TylerK07/YM3812-Module/Articles 9_SynthCard/SynthCard_YM3812.kicad_sch

## KiCad design Articles 9_SynthCard/SynthCard_YM3812.kicad_sch (2023-07-27)

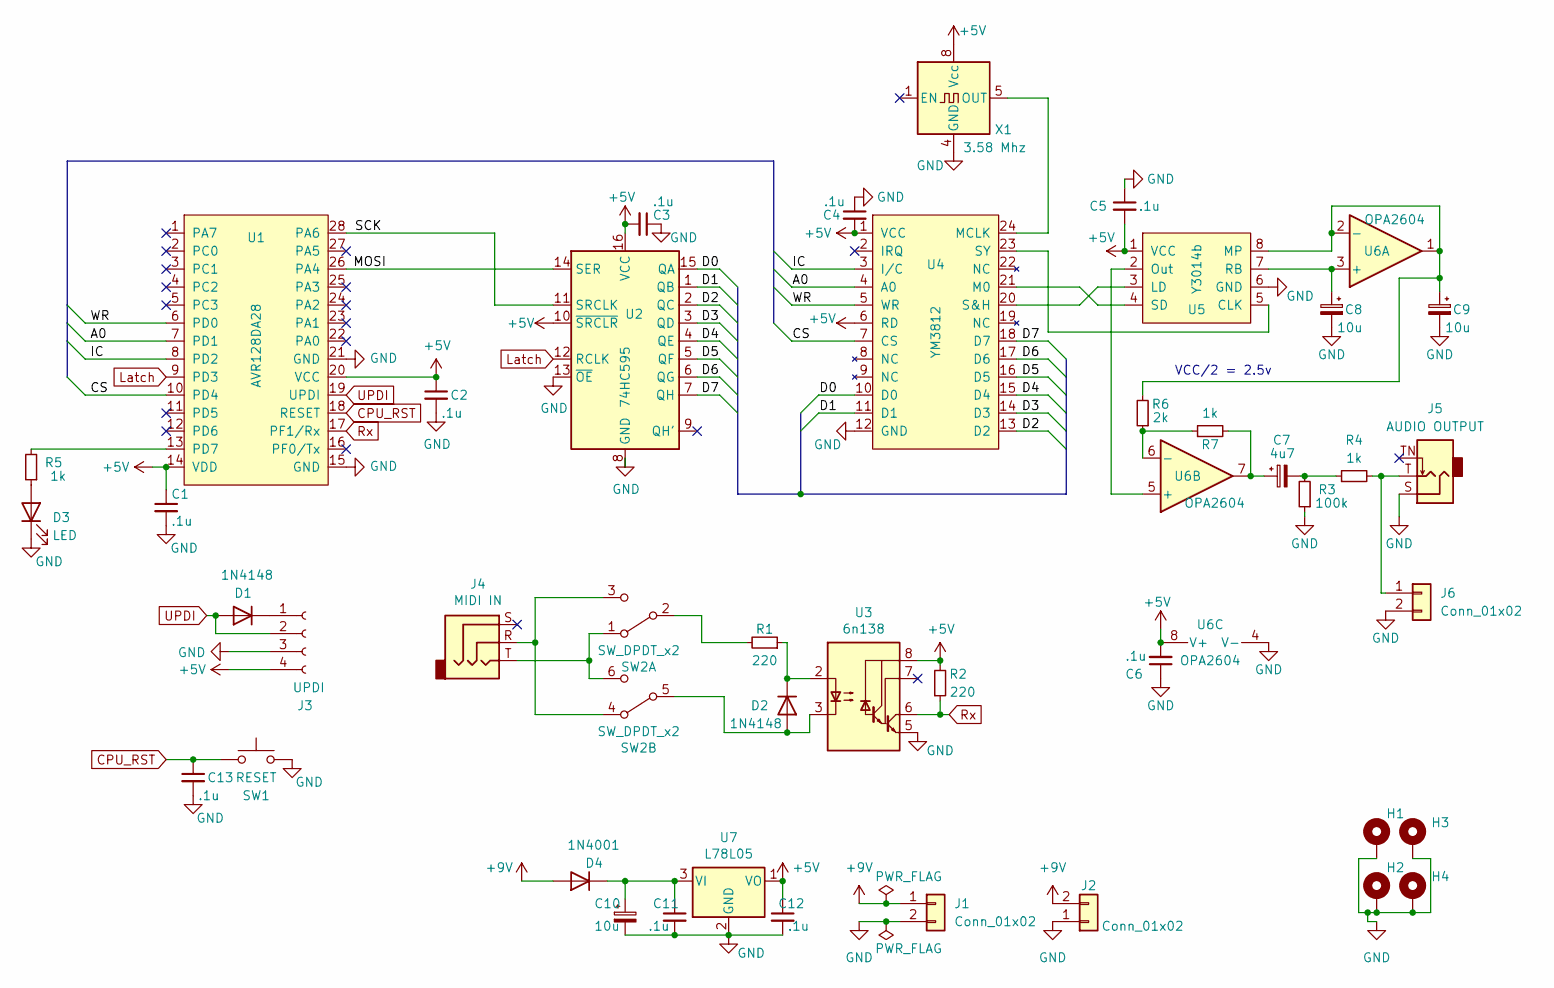
[picture p10: schematic SynthCard_YM3812.kicad_sch]

Parts:
C1, C2, C3, C4, C5, C6, C11, C12, C13: .1u; C_Disc_D6.0mm_W2.5mm_P5.00mm
C7: 4u7; CP_Radial_D5.0mm_P2.50mm
C8, C9, C10: 10u; CP_Radial_D5.0mm_P2.50mm
D1, D2: 1N4148; D_DO-35_SOD27_P7.62mm_Horizontal
D3: LED; LED_D3.0mm
D4: 1N4001; D_DO-35_SOD27_P7.62mm_Horizontal
H1, H2, H3, H4: MountingHole_Pad; MountingHole_3.2mm_M3_Pad
J1, J2: Conn_01x02; PinHeader_1x02_P2.54mm_Horizontal
J3: UPDI; PinHeader_1x04_P2.54mm_Vertical
J4: MIDI IN; StereoAudio_3.5mm
J5: AUDIO OUTPUT; MonoAudio_3.5mm_SW
J6: Conn_01x02; PinHeader_1x02_P2.54mm_Vertical
R1, R2: 220; R_Axial_DIN0207_L6.3mm_D2.5mm_P7.62mm_Horizontal
R3: 100k; R_Axial_DIN0207_L6.3mm_D2.5mm_P7.62mm_Horizontal
R4, R5, R7: 1k; R_Axial_DIN0207_L6.3mm_D2.5mm_P7.62mm_Horizontal
R6: 2k; R_Axial_DIN0207_L6.3mm_D2.5mm_P7.62mm_Horizontal
SW1: RESET; SW_PUSH_6mm
SW2: SW_DPDT_x2; SW_E-Switch_EG1271_DPDT
U1: AVR128DA28; DIP-28_W7.62mm_Socket_LongPads
U2: 74HC595; DIP-16_W7.62mm_Socket_LongPads
U3: 6n138; DIP-8_W7.62mm_LongPads
U4: YM3812; DIP-24_W15.24mm_Socket_LongPads
U5: Y3014b; DIP-8_W7.62mm_Socket_LongPads
U6: OPA2604; DIP-8_W7.62mm_Socket_LongPads
U7: L78L05; TO-92_HandSolder
X1: 3.58 Mhz; Oscillator_DIP-8

Connections:
+5V: C1.1, C2.1, C3.2, C4.2, C5.2, C6.2, C12.1, J3.4, R2.2, U1.14 (VDD), U1.20 (VCC), U2.10 (~SRCLR), U2.16 (VCC), U3.8 (VCC), U4.1 (VCC), U4.6 (RD), U5.1 (VCC), U6.8 (V+), U7.1 (VO), X1.8 (Vcc)
+9V: D4.2 (A), J1.1, J2.2
A0: U1.7 (PD1), U4.4 (A0)
CPU_RST: C13.1, SW1.2, U1.18 (RESET)
CS: U1.10 (PD4), U4.7 (CS)
D0: U2.15 (QA), U4.10 (D0)
D1: U2.1 (QB), U4.11 (D1)
D2: U2.2 (QC), U4.13 (D2)
D3: U2.3 (QD), U4.14 (D3)
D4: U2.4 (QE), U4.15 (D4)
D5: U2.5 (QF), U4.16 (D5)
D6: U2.6 (QG), U4.17 (D6)
D7: U2.7 (QH), U4.18 (D7)
GND: C1.2, C2.2, C3.1, C4.1, C5.1, C6.1, C8.2, C9.2, C10.2, C11.2, C12.2, C13.2, D3.1 (K), H1.1, H2.1, H3.1, H4.1, J1.2, J2.1, J3.3, J5.S, J6.2, R3.1, SW1.1, U1.15 (GND), U1.21 (GND), U2.8 (GND), U2.13 (~OE), U3.5 (GND), U4.12 (GND), U5.6 (GND), U6.4 (V-), U7.2 (GND), X1.4 (GND)
IC: U1.8 (PD2), U4.3 (I/C)
Latch: U1.9 (PD3), U2.12 (RCLK)
MOSI: U1.26 (PA4), U2.14 (SER)
unnamed: C7.1, R7.2, U6.7
unnamed: C7.2, R3.2, R4.1
unnamed: C8.1, U5.7 (RB), U6.3 (+)
unnamed: C9.1, R6.2, U5.8 (MP), U6.1, U6.2 (-)
unnamed: C10.1, C11.1, D4.1 (K), U7.3 (VI)
unnamed: D1.1 (K), J3.1
unnamed: D2.1 (K), R1.1, U3.2 (C1)
unnamed: D2.2 (A), SW2.5 (B), U3.3 (C2)
unnamed: D3.2 (A), R5.1
unnamed: J4.R, SW2.3 (C), SW2.4 (A)
unnamed: J4.T, SW2.1 (A), SW2.6 (C)
unnamed: J5.T, J6.1, R4.2
unnamed: R1.2, SW2.2 (B)
unnamed: R5.2, U1.13 (PD7)
unnamed: R6.1, R7.1, U6.6 (-)
unnamed: U4.20 (S&H), U5.3 (LD)
unnamed: U4.21 (M0), U5.4 (SD)
unnamed: U4.23 (SY), U5.5 (CLK)
unnamed: U4.24 (MCLK), X1.5 (OUT)
unnamed: U5.2 (Out), U6.5 (+)
Rx: R2.1, U1.17 (PF1/Rx), U3.6 (VO2)
SCK: U1.28 (PA6), U2.11 (SRCLK)
UPDI: D1.2 (A), J3.2, U1.19 (UPDI)
WR: U1.6 (PD0), U4.5 (WR)

Notes on the sheet:
VCC/2 = 2.5v
