TylerK07/YM3812-Module/Articles 10_PitchWheel/YM3812_PitchWheel/YM3812.cpp

/*
     _____.___.  _____  ________    ______  ____________
     \__  |   | /     \ \_____  \  /  __  \/_   \_____  \
      /   |   |/  \ /  \  _(__  <  >      < |   |/  ____/
      \____   /    Y    \/       \/   --   \|   /       \
      / ______\____|__  /______  /\______  /|___\_______ \
      \/              \/       \/        \/             \/
            ________ __________.____    ________
            \_____  \\______   \    |   \_____  \
             /   |   \|     ___/    |    /  ____/
            /    |    \    |   |    |___/       \
            \_______  /____|   |_______ \_______ \
                    \/                 \/       \/


YM3182 OPL2 LIBRARY source code designed to run on the AVR128DA28.
Copyright (C) 2022 Tyler Klein

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
Description:
This library wraps Yamaha's YM3812 sound processor with functions that allow for
direct manipulation of the chip's registers so you can build cool things like EuroRack modules!

*/

#include "Arduino.h"
#include <SPI.h>
#include "YM3812.h"


//Port Bits defined for control bus:
#define YM_WR    0b00000001                                                    // Pin 0, Port D - Write
#define YM_A0    0b00000010                                                    // Pin 1, Port D - Differentiates between address and data
#define YM_IC    0b00000100                                                    // Pin 2, Port D - Reset Pin
#define YM_LATCH 0b00001000                                                    // Pin 3, Port D - Output Latch
#define YM_CS    0b00010000                                                    // Pin 4, Port D - Left YM3812 Chip Select

// Optional debug light shows when information gets written to the YM3812
#define DATA_LED 0b10000000                                                    // We can use this to see activity when data is being sent

/**************
* Constructor *
**************/

YM3812::YM3812(){                                                              // Constructor
}


void YM3812::setBendRange(uint8_t wheelNoteRange){                             // Pass the number of notes in the range (even numbers please!)
  if( wheelNoteRange < 2 ) return;
  bend_note_offset = wheelNoteRange >> 1;                                      // Divide wheel range by 2 to get the offset
  bend_note_size   = PITCH_WHEEL_RANGE / (wheelNoteRange & 0xFFFE);            // Divide full range by number of notes (force to be even number of notes)
}



/************************
* Patch Functions       *
************************/

void YM3812::patchNoteOn( PatchArr &patch, uint8_t midiNote, uint8_t velocity, uint16_t pitchBend ){
  last_channel = chGetNext();
  channel_states[ last_channel ].pPatch  = &patch;                             // Store pointer to the patch
  channel_states[ last_channel ].midi_note  = midiNote;                        // Store midi note associated with the channel
  channel_states[ last_channel ].velocity = velocity;                          // Store velocity associated with the channel
  channel_states[ last_channel ].note_state = true;                            // Indicate that the note is turned on
  channel_states[ last_channel ].state_changed = millis();                     // save the time that the note was turned on

  if( pitchBend == 0x2000 ){                                                   // When not in use, do this the easy way
    channel_states[ last_channel ].bend_note = 0;                              // no pitch bend, so bend_note is just zero
    channel_states[ last_channel ].bend_rem = 0;                               // no pitch bend, so bend_rem is just zero
  } else {                                                                     // When pitchBend is set, calculate the new values
    channel_states[ last_channel ].bend_note = (pitchBend / bend_note_size) - bend_note_offset; // Calculate the whole number of semitones to bend
    channel_states[ last_channel ].bend_rem = pitchBend % bend_note_size;      // Calculate the remaining portion of a semitone to bend
  }

  chPlayNote( last_channel );                                                  // Play the note on the correct YM3812 channel
}


void YM3812::patchNoteOn( PatchArr &patch, uint8_t midiNote, uint8_t velocity ){ // If pitch bend value not passed, assume a pitch bend in the middle
  patchNoteOn( patch, midiNote, velocity, 0x2000 ); 
}


void YM3812::patchNoteOff( PatchArr &patch, uint8_t midiNote ){
  for( uint8_t ch = 0; ch<num_channels; ch++ ){
    if( channel_states[ch].pPatch == &patch ){
      if( channel_states[ch].midi_note == midiNote ){
        channel_states[ ch ].state_changed = millis();                         // Save the time that the state changed
        channel_states[ ch ].note_state = false;                               // Indicate that the note is currently off
        regKeyOn( ch, 0 );                                                     // Turn off any channels associated with the midiNote
      }
    }
  }
}

void YM3812::patchAllOff( PatchArr &patch ){
  for( uint8_t ch = 0; ch<num_channels; ch++ ){
    if( channel_states[ch].pPatch == &patch ){
      channel_states[ ch ].state_changed = millis();                           // Save the time that the state changed
      channel_states[ ch ].note_state = false;                                 // Indicate that the note is currently off
      regKeyOn( ch, 0 );                                                       // Turn off any channels associated with the midiNote
    }
  }
}

void YM3812::patchUpdate( PatchArr &patch ){                                   // Update the patch data of any active channels assocaited with the patch
  for( byte ch = 0; ch < num_channels; ch++ ){                                 // Loop through each channel
    if( channel_states[ch].pPatch == &patch ) chSendPatch( ch, patch );        // If the channel uses the patch, update the patch data on the chip
  }
}

void YM3812::patchPitchBend( PatchArr &patch, uint16_t pitchBend){             // Update the pitch of all notes associated with patch based on pitchBend
  for( byte ch = 0; ch < num_channels; ch++ ){                                 // Loop through each channel
    if( channel_states[ch].pPatch == &patch ){
      if( pitchBend == 0x2000 ){                                               // When not in use, do this the easy way
        channel_states[ ch ].bend_note = 0;                                    // no pitch bend, so bend_note is just zero
        channel_states[ ch ].bend_rem = 0;                                     // no pitch bend, so bend_rem is just zero
      } else {                                                                 // When pitchBend is set, calculate the new values
        channel_states[ ch ].bend_note = (pitchBend / bend_note_size) - bend_note_offset; // Calculate the whole number of semitones to bend
        channel_states[ ch ].bend_rem = pitchBend % bend_note_size;            // Calculate the remaining portion of a semitone to bend
      }
      chSetPitch(ch);
    }
  }
}


/************************
* Channel Functions     *
************************/

// chSendPatch Theory of Operation:
// This function is the heart of the class, and without too many modifications can be updated to work with any of the
// Yamaha synthesis chips. The function accepts a generalized patch array with values in order according to the
// indicies outlined in YMDefs.h. Because all values in the array are between 0 and 127, this function scales
// those values to the correct bit depth, combines them with other values to produce the correct combinations for the register
// map of the YM3812 and then sends them to the sound chip.

void YM3812::chSendPatch( byte ch, PatchArr &patch ){
  uint8_t  mem_offset, patch_offset;
  uint8_t  op_level;

  //Channel Settings
  sendData( 0xC0+ch,  ((patch[PATCH_FEEDBACK]>>4)<<1) |                        // Compose the feedback and Algorithm values
                       (patch[PATCH_ALGORITHM]>>6)    );                       // into a single byte and send to YM3812

  for( uint8_t op = 0; op<2; op++ ){
    mem_offset = op_map[channel_map[ch] + op*3];                               // Determine memory offset for slot 1 for the channel
    patch_offset = PATCH_OP_SETTINGS * op;                                     // Determine operator's index offset for the patch properties 

    if( (patch[PATCH_ALGORITHM] == 0) && (op==0) ){
      op_level = patch[patch_offset + PATCH_LEVEL] >> 1;
    } else {
      op_level = 63-( ( (127 - patch[patch_offset + PATCH_LEVEL]) * channel_states[ ch ].velocity ) >> 8);
    }

    sendData( 0x20+mem_offset,      ((patch[patch_offset + PATCH_TREMOLO        ]>>6)<<7) |  // Compose Tremolo, vibrato, percussive envelope
                                    ((patch[patch_offset + PATCH_VIBRATO        ]>>6)<<6) |  // envelope scaling flags along with frequency
                                    ((patch[patch_offset + PATCH_PERCUSSIVE_ENV ]>>6)<<5) |  // multiple into a single 8-bit register value
                                    ((patch[patch_offset + PATCH_ENV_SCALING    ]>>6)<<4) |  // and send to the YM3812
                                    ((patch[patch_offset + PATCH_FREQUENCY_MULT ]>>3)<<0) );

    sendData( 0x40+mem_offset,      ((patch[patch_offset + PATCH_LEVEL_SCALING ]>>5)<<6)  |  // Compose level scaling and level value for the
                                      op_level                                            ); // output channel and send to the YM3812
    sendData( 0x60+mem_offset,      ((patch[patch_offset + PATCH_ATTACK        ]>>3)<<4)  |  // Compose attack and decay settings into a single
                                    ((patch[patch_offset + PATCH_DECAY         ]>>3)<<0)  ); // 8-bit register and send to YM3812
    sendData( 0x80+mem_offset, ((0xF-(patch[patch_offset + PATCH_SUSTAIN_LEVEL ]>>3))<<4) |  // Compose sustain level (inverted) and release rate settings into a single
                                    ((patch[patch_offset + PATCH_RELEASE_RATE  ]>>3)<<0) );  // 8-bit register and send to YM3812
    sendData( 0xE0+mem_offset,      ((patch[patch_offset + PATCH_WAVEFORM      ]>>5)<<0) );  // Send waveform register to YM3812
  }

}

uint8_t YM3812::chGetNext(){
  uint8_t on_channel = 0xFF;                                                   // The channel that has been on the longest 
  uint8_t off_channel = 0xFF;                                                  // The channel that has been OFF the longest
  unsigned long oldest_on_time = millis(); 
  unsigned long oldest_off_time = millis(); 

  for( uint8_t ch=0; ch < num_channels; ch++ ){                                // Loop through all of the channels
    if( channel_states[ch].note_state ){                                       // If the note is turned on...
      if( channel_states[ch].state_changed < oldest_on_time ){                 // Is this the longest running note?
        oldest_on_time = channel_states[ch].state_changed;                     // save the current time
        on_channel = ch;                                                       // save this as our longest running channel
      } 
    } else {                                                                   // If the note is turned off...
      if( channel_states[ch].state_changed < oldest_off_time ){                // Is this the longest turned off note?
        oldest_off_time = channel_states[ch].state_changed;                    // save the current time
        off_channel = ch;                                                      // save this as our longest off channel
      } 
    }
  }

  if( off_channel < 0xFF ){                                                    // If it isn't FF, then we changed... so at least one channel is currently off.
    return( off_channel );                                                     // Return the channel that has been off the longest
  }
  return( on_channel );                                                        // Return the channel that has been ON the longest
}

void YM3812::chSetPitch( uint8_t ch ){
  uint8_t block, fNumIndex;
  uint8_t midiNote = channel_states[ch].midi_note+channel_states[ch].bend_note;// Calculate the midiNote based on the pitchBend data for the midi channel

  if( midiNote > 127 ) midiNote = 0;                                           // If midiNote wrapped around, then PB went below midiNote zero
  if( midiNote > 113 ) return;                                                 // Ignore any midi notes outside the range of the chip
  
  if( midiNote < 18 ){                                                         // For case where midi note is less than our repeating range
    block = 0;                                                                 // Block will always be zero
    fNumIndex = midiNote;                                                      // The midiNote will be the index of the FREQ_SCALE array
  } else {                                                                     // 
    block = (midiNote - 18) / 12;                                              // Calculate the block based on the octave of the note
    fNumIndex = ((midiNote - 18) % 12) + 18;                                   // Calculate the fNum of the note
  }

  uint16_t lFNum = FRQ_SCALE[fNumIndex];
  uint16_t hFNum = FRQ_SCALE[fNumIndex+1];
  uint16_t FNum = (uint32_t(hFNum - lFNum) * uint32_t(channel_states[ch].bend_rem)) / bend_note_size + lFNum;

  regFrqBlock( ch, block );                                                    // Send block number to chip
  regFrqFnum(  ch, FNum  );                                                    // Send F-Number to chip
}

void YM3812::chPlayNote( uint8_t ch ){                                         // Play a note on channel ch with pitch midiNote
  //Assumes that midi note and pitch bend properties were all set before running this function
  regKeyOn( ch, 0 );                                                           // Turn off the channel if it is on
  chSendPatch( ch, *channel_states[ch].pPatch );                               // Send the patch to the YM3812
  chSetPitch( ch );                                                            // Set the pitch of the note (pitch info stored in channel_states array)
  regKeyOn( ch, 1 );                                                           // Turn the channel back on
}



/********************************
* Processor Control Functions   *
********************************/

void YM3812::reset(){
  PORTD.DIRSET = YM_IC | YM_A0 | YM_WR | YM_LATCH | YM_CS | DATA_LED;          // Set control lines high to output mode

  PORTD.OUTCLR = YM_LATCH;                                                     // Set the latch low to start
  PORTD.OUTSET = YM_WR | YM_CS;                                                // Set chip select and write lines high
  PORTD.OUTCLR = DATA_LED;                                                     // Turn the data LED off
  
  //Hard Reset the YM3812
  PORTD.OUTCLR = YM_IC; delay(10);                                             // Hard Reset the processor by bringing Initialize / Clear line low
  PORTD.OUTSET = YM_IC; delay(10);                                             // Complete process by bringing line high and allowing a short moment to reset

  SPI.begin();


  //Clear all of our register caches
  reg_01 = reg_08 = reg_BD = 0;                                                // Clear out global settings
  for( uint8_t ch = 0; ch < YM3812_NUM_CHANNELS; ch++ ){                       // Loop through all of the channels
    reg_A0[ch] = reg_B0[ch] = 0;                                               // Set all register info to zero
  }
  regWaveset( 1 );                                                             // Enable all wave forms (not just sine waves)
}

void YM3812::sendData( uint8_t reg, uint8_t val ){
  PORTD.OUTSET = DATA_LED;

  PORTD.OUTCLR = YM_CS;                                                        // Enable the chip
  PORTD.OUTCLR = YM_A0;                                                        // Put chip into register select mode

  SPI.transfer(reg);                                                           // Put register location onto the data bus through SPI port
  PORTD.OUTSET = YM_LATCH;                                                     // Latch register location into the 74HC595
  delayMicroseconds(1);                                                        // wait a tic.
  PORTD.OUTCLR = YM_LATCH;                                                     // Bring latch low now that the location is latched

  PORTD.OUTCLR = YM_WR;                                                        // Bring write low to begin the write cycle
  delayMicroseconds(10);                                                       // Delay so chip completes write cycle
  PORTD.OUTSET = YM_WR;                                                        // Bring write high
  delayMicroseconds(10);                                                       // Delay until the chip is ready to continue

  PORTD.OUTSET = YM_A0;                                                        // Put chip into data write mode

  SPI.transfer(val);                                                           // Put value onto the data bus through SPI port
  PORTD.OUTSET = YM_LATCH;                                                     // Latch the value into the 74HC595
  delayMicroseconds(1);                                                        // wait a tic.
  PORTD.OUTCLR = YM_LATCH;                                                     // Bring latch low now that the value is latched

  PORTD.OUTCLR = YM_WR;                                                        // Bring write low to begin the write cycle
  delayMicroseconds(10);                                                       // Delay so chip completes write cycle
  PORTD.OUTSET = YM_WR;                                                        // Bring write high
  delayMicroseconds(10);                                                       // Delay until the chip is ready to continue

  PORTD.OUTSET = YM_CS;                                                        // Bring Chip Select high to disable the YM3812

  PORTD.OUTCLR = DATA_LED;

}
