TylerK07/YM3812-Module/Articles 10_PitchWheel/YM3812_PitchWheel/instruments.h

#ifndef INSTRUMENTS_H
#define INSTRUMENTS_H
const unsigned char ym_patch_0[78] PROGMEM = {0x22,0x00,0x00,0x00,0x00,0x00,0x50,0x00,0x00,0x00,0x20,0x1E,0x60,0x00,0x40,0x78,0x00,0x78,0x00,0x20,0x00,0x00,0x08,0x00,0x00,0x00,0x00,0x00,0x00,0x00,0x00,0x00,0x78,0x20,0x10,0x00,0x30,0x00,0x00,0x08,0x00,0x00,0x00,0x00,0x00,0x7E,0x00,0x00,0x00,0x00,0x00,0x00,0x00,0x00,0x00,0x00,0x00,0x00,0x00,0x00,0x00,0x00,0x7E,0x00,0x00,0x00,0x00,0x00,0x00,0x00,0x00,0x00,0x00,0x00,0x00,0x00,0x00,0x00}; // Acoustic Grand Piano
const unsigned char ym_patch_1[78] PROGMEM = {0x22,0x00,0x00,0x00,0x00,0x00,0x00,0x00,0x00,0x00,0x20,0x0E,0x60,0x00,0x40,0x78,0x00,0x78,0x00,0x20,0x00,0x00,0x08,0x00,0x00,0x00,0x00,0x00,0x00,0x00,0x00,0x00,0x78,0x20,0x10,0x00,0x30,0x00,0x00,0x08,0x00,0x00,0x00,0x00,0x00,0x7E,0x00,0x00,0x00,0x00,0x00,0x00,0x00,0x00,0x00,0x00,0x00,0x00,0x00,0x00,0x00,0x00,0x7E,0x00,0x00,0x00,0x00,0x00,0x00,0x00,0x00,0x00,0x00,0x00,0x00,0x00,0x00,0x00}; // Bright Acoustic Piano
const unsigned char ym_patch_2[78] PROGMEM = {0x22,0x00,0x00,0x00,0x00,0x00,0x50,0x00,0x00,0x00,0x00,0x36,0x00,0x00,0x40,0x78,0x00,0x78,0x00,0x20,0x00,0x00,0x08,0x00,0x00,0x00,0x00,0x00,0x00,0x00,0x00,0x00,0x78,0x20,0x10,0x00,0x30,0x00,0x00,0x08,0x00,0x00,0x00,0x00,0x00,0x7E,0x00,0x00,0x00,0x00,0x00,0x00,0x00,0x00,0x00,0x00,0x00,0x00,0x00,0x00,0x00,0x00,0x7E,0x00,0x00,0x00,0x00,0x00,0x00,0x00,0x00,0x00,0x00,0x00,0x00,0x00,0x00,0x00}; // Electric Grand Piano
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
const unsigned char ym_patch_174[78] PROGMEM = {0x22,0x3F,0x00,0x00,0x00,0x00,0x00,0x00,0x00,0x00,0x40,0x00,0x40,0x00,0x00,0x78,0x78,0x40,0x00,0x78,0x00,0x00,0x30,0x00,0x00,0x00,0x00,0x40,0x14,0x00,0x00,0x00,0x78,0x00,0x78,0x00,0x20,0x00,0x00,0x48,0x00,0x00,0x00,0x00,0x00,0x7E,0x00,0x00,0x00,0x00,0x00,0x00,0x00,0x00,0x00,0x00,0x00,0x00,0x00,0x00,0x00,0x00,0x7E,0x00,0x00,0x00,0x00,0x00,0x00,0x00,0x00,0x00,0x00,0x00,0x00,0x00,0x00,0x00}; // Open Triangle
const unsigned char *patches[] = {
ym_patch_0,ym_patch_1,ym_patch_2,ym_patch_3,ym_patch_4,ym_patch_5,ym_patch_6,ym_patch_7,ym_patch_8,ym_patch_9,ym_patch_10,ym_patch_11,ym_patch_12,ym_patch_13,ym_patch_14,ym_patch_15,ym_patch_16,ym_patch_17,ym_patch_18,ym_patch_19,ym_patch_20,ym_patch_21,ym_patch_22,ym_patch_23,ym_patch_24,ym_patch_25,ym_patch_26,ym_patch_27,ym_patch_28,ym_patch_29,ym_patch_30,ym_patch_31,ym_patch_32,ym_patch_33,ym_patch_34,ym_patch_35,ym_patch_36,ym_patch_37,ym_patch_38,ym_patch_39,ym_patch_40,ym_patch_41,ym_patch_42,ym_patch_43,ym_patch_44,ym_patch_45,ym_patch_46,ym_patch_47,ym_patch_48,ym_patch_49,ym_patch_50,ym_patch_51,ym_patch_52,ym_patch_53,ym_patch_54,ym_patch_55,ym_patch_56,ym_patch_57,ym_patch_58,ym_patch_59,ym_patch_60,ym_patch_61,ym_patch_62,ym_patch_63,ym_patch_64,ym_patch_65,ym_patch_66,ym_patch_67,ym_patch_68,ym_patch_69,ym_patch_70,ym_patch_71,ym_patch_72,ym_patch_73,ym_patch_74,ym_patch_75,ym_patch_76,ym_patch_77,ym_patch_78,ym_patch_79,ym_patch_80,ym_patch_81,ym_patch_82,ym_patch_83,ym_patch_84,ym_patch_85,ym_patch_86,ym_patch_87,ym_patch_88,ym_patch_89,ym_patch_90,ym_patch_91,ym_patch_92,ym_patch_93,ym_patch_94,ym_patch_95,ym_patch_96,ym_patch_97,ym_patch_98,ym_patch_99,ym_patch_100,ym_patch_101,ym_patch_102,ym_patch_103,ym_patch_104,ym_patch_105,ym_patch_106,ym_patch_107,ym_patch_108,ym_patch_109,ym_patch_110,ym_patch_111,ym_patch_112,ym_patch_113,ym_patch_114,ym_patch_115,ym_patch_116,ym_patch_117,ym_patch_118,ym_patch_119,ym_patch_120,ym_patch_121,ym_patch_122,ym_patch_123,ym_patch_124,ym_patch_125,ym_patch_126,ym_patch_127,ym_patch_128,ym_patch_129,ym_patch_130,ym_patch_131,ym_patch_132,ym_patch_133,ym_patch_134,ym_patch_135,ym_patch_136,ym_patch_137,ym_patch_138,ym_patch_139,ym_patch_140,ym_patch_141,ym_patch_142,ym_patch_143,ym_patch_144,ym_patch_145,ym_patch_146,ym_patch_147,ym_patch_148,ym_patch_149,ym_patch_150,ym_patch_151,ym_patch_152,ym_patch_153,ym_patch_154,ym_patch_155,ym_patch_156,ym_patch_157,ym_patch_158,ym_patch_159,ym_patch_160,ym_patch_161,ym_patch_162,ym_patch_163,ym_patch_164,ym_patch_165,ym_patch_166,ym_patch_167,ym_patch_168,ym_patch_169,ym_patch_170,ym_patch_171,ym_patch_172,ym_patch_173,ym_patch_174,};
const char PName0[] PROGMEM = "Acoustic Grand Piano";
const char PName1[] PROGMEM = "Bright Acoustic Piano";
const char PName2[] PROGMEM = "Electric Grand Piano";
const char PName3[] PROGMEM = "Honky-tonk Piano";
const char PName4[] PROGMEM = "Electric Piano 1";
const char PName5[] PROGMEM = "Electric Piano 2";
const char PName6[] PROGMEM = "Harpsichord";
const char PName7[] PROGMEM = "Clavi";
const char PName8[] PROGMEM = "Celesta";
const char PName9[] PROGMEM = "Glockenspiel";
const char PName10[] PROGMEM = "Music Box";
const char PName11[] PROGMEM = "Vibraphone";
const char PName12[] PROGMEM = "Marimba";
const char PName13[] PROGMEM = "Xylophone";
const char PName14[] PROGMEM = "Tubular Bells";
const char PName15[] PROGMEM = "Dulcimer";
const char PName16[] PROGMEM = "Hammond Organ";
const char PName17[] PROGMEM = "Percussive Organ";
const char PName18[] PROGMEM = "Rock Organ";
const char PName19[] PROGMEM = "Church Organ";
const char PName20[] PROGMEM = "Reed Organ";
const char PName21[] PROGMEM = "Accordion";
const char PName22[] PROGMEM = "Harmonica";
const char PName23[] PROGMEM = "Tango Accordion";
const char PName24[] PROGMEM = "Guitar Nylon";
const char PName25[] PROGMEM = "Guitar Steel";
const char PName26[] PROGMEM = "Electric Guitar (jazz)";
const char PName27[] PROGMEM = "Electric Guitar (clean)";
const char PName28[] PROGMEM = "Electric Guitar (muted))";
const char PName29[] PROGMEM = "Overdriven Guitar";
const char PName30[] PROGMEM = "Distortion Guitar";
const char PName31[] PROGMEM = "Guitar Harmonics";
const char PName32[] PROGMEM = "Acoustic Bass";
const char PName33[] PROGMEM = "Electric Bass (finger)";
const char PName34[] PROGMEM = "Electric Bass (pick)";
const char PName35[] PROGMEM = "Fretless Bass";
const char PName36[] PROGMEM = "Slap Bass 1";
const char PName37[] PROGMEM = "Slap Bass 2";
const char PName38[] PROGMEM = "Synth Bass 1";
const char PName39[] PROGMEM = "Synth Bass 2";
const char PName40[] PROGMEM = "Violin";
const char PName41[] PROGMEM = "Viola";
const char PName42[] PROGMEM = "Cello";
const char PName43[] PROGMEM = "Contrabass";
const char PName44[] PROGMEM = "Tremolo Strings";
const char PName45[] PROGMEM = "Pizzicato Strings";
const char PName46[] PROGMEM = "Orchestral Harp";
const char PName47[] PROGMEM = "Timpani";
const char PName48[] PROGMEM = "String Ensembles 1";
const char PName49[] PROGMEM = "String Ensembles 2";
const char PName50[] PROGMEM = "Synth Strings 1";
const char PName51[] PROGMEM = "Synth Strings 2";
const char PName52[] PROGMEM = "Choir Aahs";
const char PName53[] PROGMEM = "Voice Oohs";
const char PName54[] PROGMEM = "Synth Voice";
const char PName55[] PROGMEM = "Orchestra Hit";
const char PName56[] PROGMEM = "Trumpet";
const char PName57[] PROGMEM = "Trombone";
const char PName58[] PROGMEM = "Tuba";
const char PName59[] PROGMEM = "Muted Trumpet";
const char PName60[] PROGMEM = "French Horn";
const char PName61[] PROGMEM = "Brass Section";
const char PName62[] PROGMEM = "Synth Brass 1";
const char PName63[] PROGMEM = "Synth Bass 2";
const char PName64[] PROGMEM = "Soprano Sax";
const char PName65[] PROGMEM = "Alto Sax";
const char PName66[] PROGMEM = "Tenor Sax";
const char PName67[] PROGMEM = "Baritone Sax";
const char PName68[] PROGMEM = "Oboe";
const char PName69[] PROGMEM = "English Horn";
const char PName70[] PROGMEM = "Bassoon";
const char PName71[] PROGMEM = "Clarinet";
const char PName72[] PROGMEM = "Piccolo";
const char PName73[] PROGMEM = "Flute";
const char PName74[] PROGMEM = "Recorder";
const char PName75[] PROGMEM = "Pan Flute";
const char PName76[] PROGMEM = "Bottle Blow";
const char PName77[] PROGMEM = "Shakuhachi";
const char PName78[] PROGMEM = "Whistle";
const char PName79[] PROGMEM = "Ocarina";
const char PName80[] PROGMEM = "Lead 1 (Square)";
const char PName81[] PROGMEM = "Lead 2 (sawtooth)";
const char PName82[] PROGMEM = "Lead 3 (calliope)";
const char PName83[] PROGMEM = "Lead 4 (chiffer)";
const char PName84[] PROGMEM = "Lead 5 (charang)";
const char PName85[] PROGMEM = "Lead 6 (voice)";
const char PName86[] PROGMEM = "Lead 7 (5th sawtooth)";
const char PName87[] PROGMEM = "Lead 8 (bass+Lead)";
const char PName88[] PROGMEM = "Pad 1 (New Age)";
const char PName89[] PROGMEM = "Pad 2 (warm)";
const char PName90[] PROGMEM = "Pad 3 (polysynth)";
const char PName91[] PROGMEM = "Pad 4 (choir)";
const char PName92[] PROGMEM = "Pad 5 (bowed glass)";
const char PName93[] PROGMEM = "Pad 6 (metal)";
const char PName94[] PROGMEM = "Pad 7 (Halo)";
const char PName95[] PROGMEM = "Pad 8 (sweep)";
const char PName96[] PROGMEM = "FX 1 (rain)";
const char PName97[] PROGMEM = "FX2 (soundtrack)";
const char PName98[] PROGMEM = "FX 3 (crystal)";
const char PName99[] PROGMEM = "FX 4 (atmosphere)";
const char PName100[] PROGMEM = "FX 5 (brightness)";
const char PName101[] PROGMEM = "FX 6 (goblin)";
const char PName102[] PROGMEM = "FX 7 (echo drops)";
const char PName103[] PROGMEM = "FX 8 (star-theme)";
const char PName104[] PROGMEM = "Sitar";
const char PName105[] PROGMEM = "Banjo";
const char PName106[] PROGMEM = "Shamisen";
const char PName107[] PROGMEM = "Koto";
const char PName108[] PROGMEM = "Kalimba";
const char PName109[] PROGMEM = "Bag Pipe";
const char PName110[] PROGMEM = "Fiddle";
const char PName111[] PROGMEM = "Shanai";
const char PName112[] PROGMEM = "Tinkle Bell";
const char PName113[] PROGMEM = "Agogo";
const char PName114[] PROGMEM = "Steel Drums";
const char PName115[] PROGMEM = "Woodblock";
const char PName116[] PROGMEM = "Taiko Drum";
const char PName117[] PROGMEM = "Melodic Tom";
const char PName118[] PROGMEM = "Synth Drum";
const char PName119[] PROGMEM = "Reverse Cymbal";
const char PName120[] PROGMEM = "Guitar Fret Noise";
const char PName121[] PROGMEM = "Breath Noise";
const char PName122[] PROGMEM = "Seashore";
const char PName123[] PROGMEM = "Bird Tweet";
const char PName124[] PROGMEM = "Telephone Ring";
const char PName125[] PROGMEM = "Helicopter";
const char PName126[] PROGMEM = "Applause";
const char PName127[] PROGMEM = "Gun Shot";
const char PName128[] PROGMEM = "Acoustic Bass Drum";
const char PName129[] PROGMEM = "Acoustic Bass Drum";
const char PName130[] PROGMEM = "Slide Stick";
const char PName131[] PROGMEM = "Acoustic Snare";
const char PName132[] PROGMEM = "Hand Clap";
const char PName133[] PROGMEM = "Electric Snare";
const char PName134[] PROGMEM = "Low Floor Tom";
const char PName135[] PROGMEM = "Closed High-Hat";
const char PName136[] PROGMEM = "High Floor Tom";
const char PName137[] PROGMEM = "Pedal High Hat";
const char PName138[] PROGMEM = "Low Tom";
const char PName139[] PROGMEM = "Open High Hat";
const char PName140[] PROGMEM = "Low-Mid Tom";
const char PName141[] PROGMEM = "High-mid Tom";
const char PName142[] PROGMEM = "Crash Cymbal 1";
const char PName143[] PROGMEM = "High Tom";
const char PName144[] PROGMEM = "Ride Cymbal 1";
const char PName145[] PROGMEM = "Chinses Cymbal";
const char PName146[] PROGMEM = "Ride Bell";
const char PName147[] PROGMEM = "Tambourine";
const char PName148[] PROGMEM = "Splash Cymbal";
const char PName149[] PROGMEM = "Cowbell";
const char PName150[] PROGMEM = "Crash Cymbal 2";
const char PName151[] PROGMEM = "Vibraslap";
const char PName152[] PROGMEM = "Ride Cymbal 2";
const char PName153[] PROGMEM = "High Bongo";
const char PName154[] PROGMEM = "Low Bango";
const char PName155[] PROGMEM = "Mute High Conga";
const char PName156[] PROGMEM = "Open High Conga";
const char PName157[] PROGMEM = "Low Conga";
const char PName158[] PROGMEM = "High Timbale";
const char PName159[] PROGMEM = "Low Timbale";
const char PName160[] PROGMEM = "High Agogo";
const char PName161[] PROGMEM = "Low Agogo";
const char PName162[] PROGMEM = "Cabasa";
const char PName163[] PROGMEM = "Maracas";
const char PName164[] PROGMEM = "Short Whistle";
const char PName165[] PROGMEM = "Long Whistle";
const char PName166[] PROGMEM = "Short Guiro";
const char PName167[] PROGMEM = "Long Guiro";
const char PName168[] PROGMEM = "Claves";
const char PName169[] PROGMEM = "High Wood Block";
const char PName170[] PROGMEM = "Low Wood Block";
const char PName171[] PROGMEM = "Mute Cuica";
const char PName172[] PROGMEM = "Open Cuica";
const char PName173[] PROGMEM = "Mute Triangle";
const char PName174[] PROGMEM = "Open Triangle";
const char* const patchNames[] = {PName0,PName1,PName2,PName3,PName4,PName5,PName6,PName7,PName8,PName9,PName10,PName11,PName12,PName13,PName14,PName15,PName16,PName17,PName18,PName19,PName20,PName21,PName22,PName23,PName24,PName25,PName26,PName27,PName28,PName29,PName30,PName31,PName32,PName33,PName34,PName35,PName36,PName37,PName38,PName39,PName40,PName41,PName42,PName43,PName44,PName45,PName46,PName47,PName48,PName49,PName50,PName51,PName52,PName53,PName54,PName55,PName56,PName57,PName58,PName59,PName60,PName61,PName62,PName63,PName64,PName65,PName66,PName67,PName68,PName69,PName70,PName71,PName72,PName73,PName74,PName75,PName76,PName77,PName78,PName79,PName80,PName81,PName82,PName83,PName84,PName85,PName86,PName87,PName88,PName89,PName90,PName91,PName92,PName93,PName94,PName95,PName96,PName97,PName98,PName99,PName100,PName101,PName102,PName103,PName104,PName105,PName106,PName107,PName108,PName109,PName110,PName111,PName112,PName113,PName114,PName115,PName116,PName117,PName118,PName119,PName120,PName121,PName122,PName123,PName124,PName125,PName126,PName127,PName128,PName129,PName130,PName131,PName132,PName133,PName134,PName135,PName136,PName137,PName138,PName139,PName140,PName141,PName142,PName143,PName144,PName145,PName146,PName147,PName148,PName149,PName150,PName151,PName152,PName153,PName154,PName155,PName156,PName157,PName158,PName159,PName160,PName161,PName162,PName163,PName164,PName165,PName166,PName167,PName168,PName169,PName170,PName171,PName172,PName173,PName174,};
#define NUM_MELODIC       128
#define NUM_DRUMS         47
#endif
